knivd/16z/graphics/P1010034.JPG

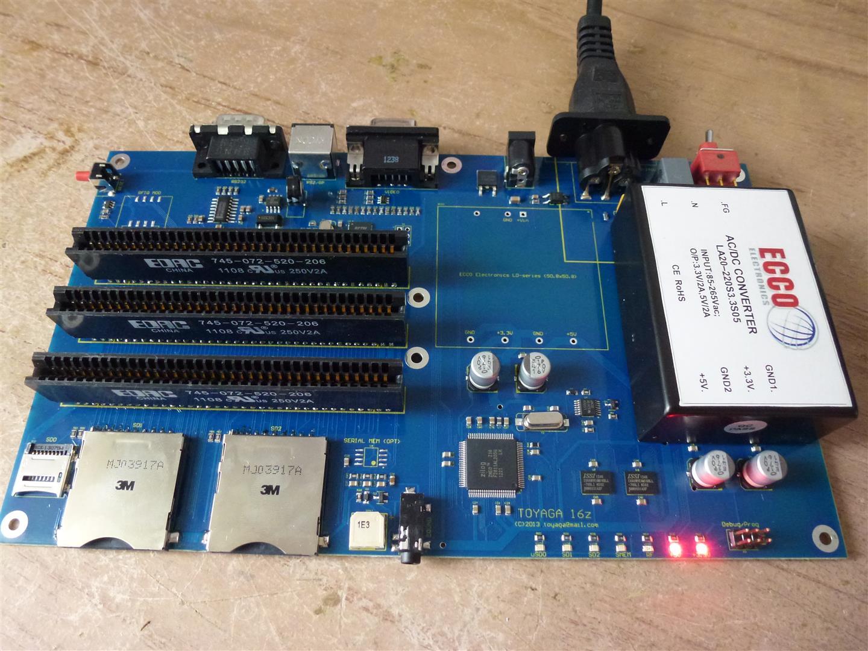
graphics/P1010034.JPG
