knivd/16z/graphics/P1010167.JPG

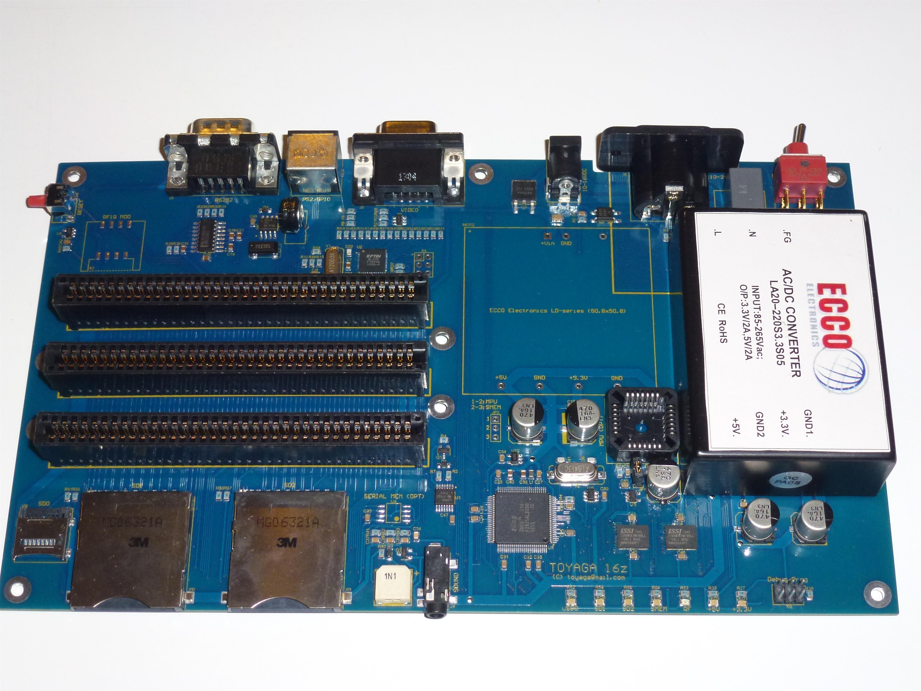
graphics/P1010167.JPG
