knivd/16z/graphics/P1010169.JPG

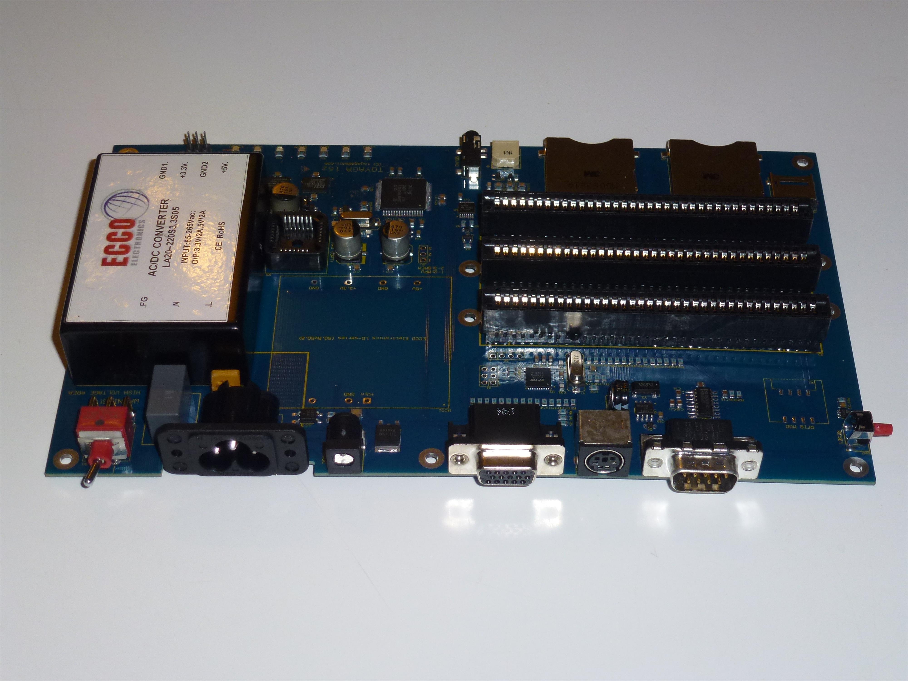
graphics/P1010169.JPG
