knivd/16z/graphics/P1010174.JPG

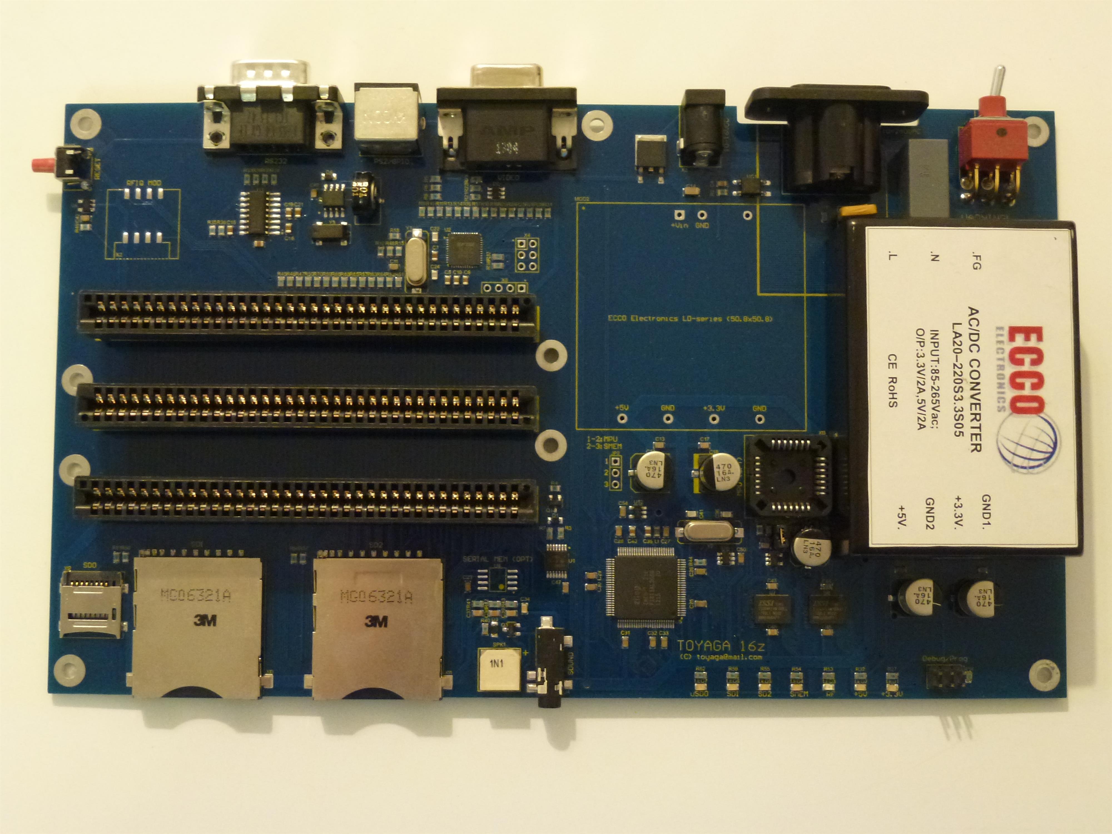
graphics/P1010174.JPG
