knivd/16z/graphics/P1010176.JPG

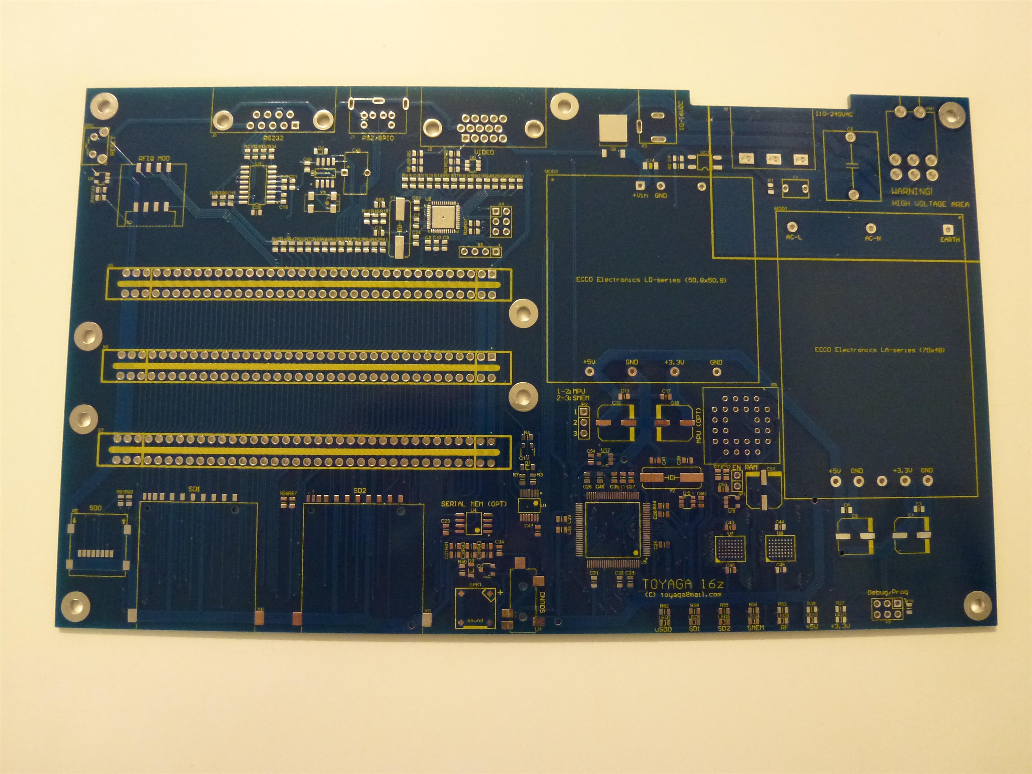
graphics/P1010176.JPG
