knivd/16z/graphics/P1010178.JPG

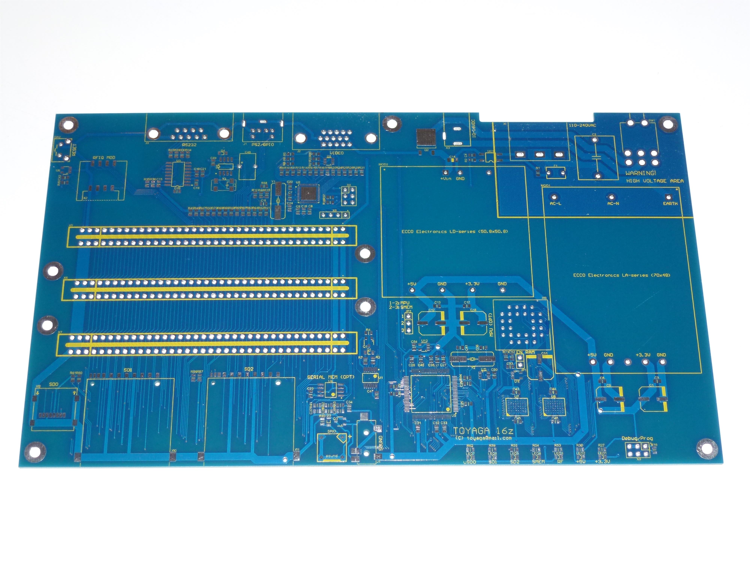
graphics/P1010178.JPG
