knivd/16z/graphics/P1010181.JPG

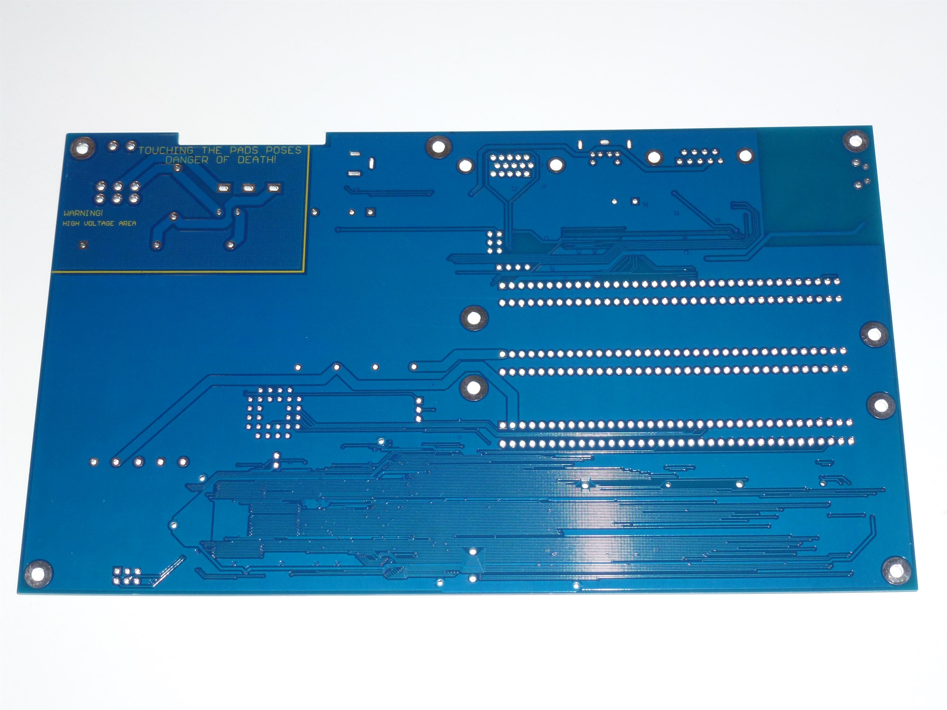
graphics/P1010181.JPG
